SchneHa/Gas_Meter/Gas_Meter/src/Gaszaehler_CP/Gas_MQTT.h

//#include "picoMQTT.h"
//
PicoMQTT::Client mqtt( "xxx.xxx.xxx.xxx" );
String    MQTT_command        = "";                // commands for Counter
String    topic               = "Energy/Gas/";
//
//
//
void setup_MQTT( ) 
{
//
// Subscribe to MQTT commands
//
   mqtt.subscribe( topic + "command", [](const char * topic, const char* payload ) 
   {
       // payload might be binary, but PicoMQTT guarantees that it's zero-terminated
       Serial.printf( "Received message in topic '%s': %s\n", topic, payload );
       MQTT_command = payload ;
   });
    mqtt.begin();
}

void publish_topic( String subtopic, String message ) 
{
//
   String  topic1 = topic + subtopic;
   Serial.printf( "Publishing message in topic '%30s': %15s\n", topic1.c_str( ), message.c_str( ) );
   mqtt.publish( topic1, message );
   delay( 100 );
}
